loganwilliams/thermografree/docs/images/demo2.jpg

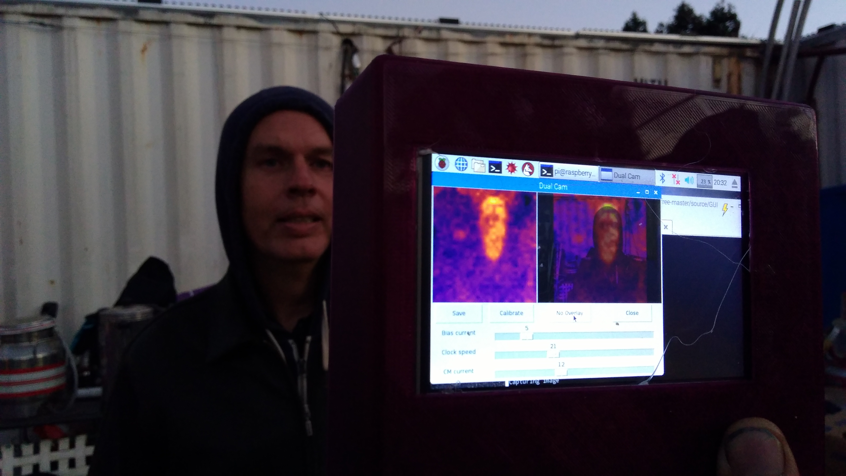
docs/images/demo2.jpg
